aalonsopuig/Retrobot/Media/Foto 16-07-11 15 34 50.jpeg

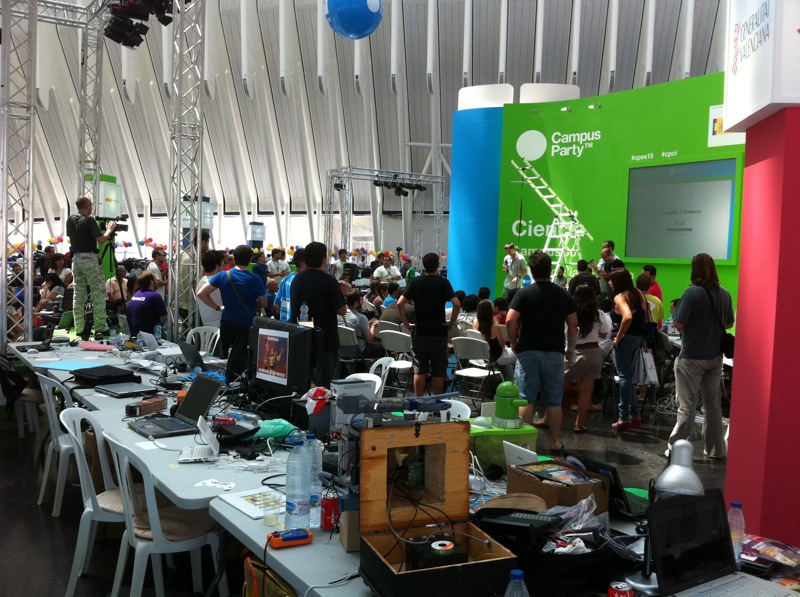
Media/Foto 16-07-11 15 34 50.jpeg
