aalonsopuig/Retrobot/Media/Foto 16-07-11 15 41 18.jpeg

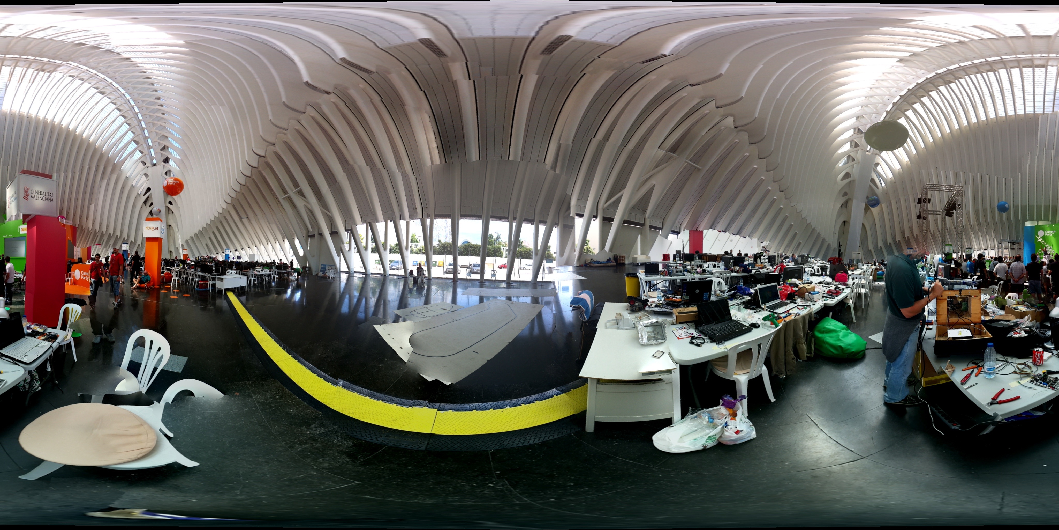
Media/Foto 16-07-11 15 41 18.jpeg
