aalonsopuig/Retrobot/Media/Foto 18-07-11 12 18 01.jpeg

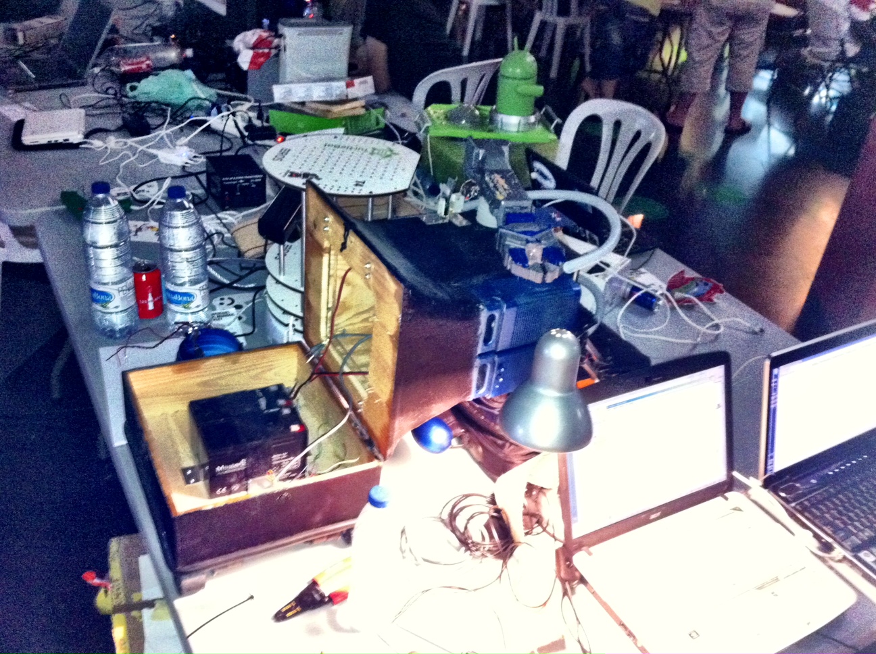
Media/Foto 18-07-11 12 18 01.jpeg
