aalonsopuig/Retrobot/Media/FotoEnCampus.jpg

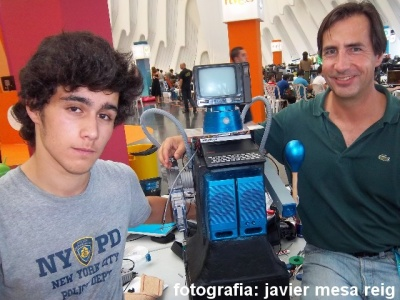
Media/FotoEnCampus.jpg
