aalonsopuig/Retrobot/Media/Imagen 099.jpg

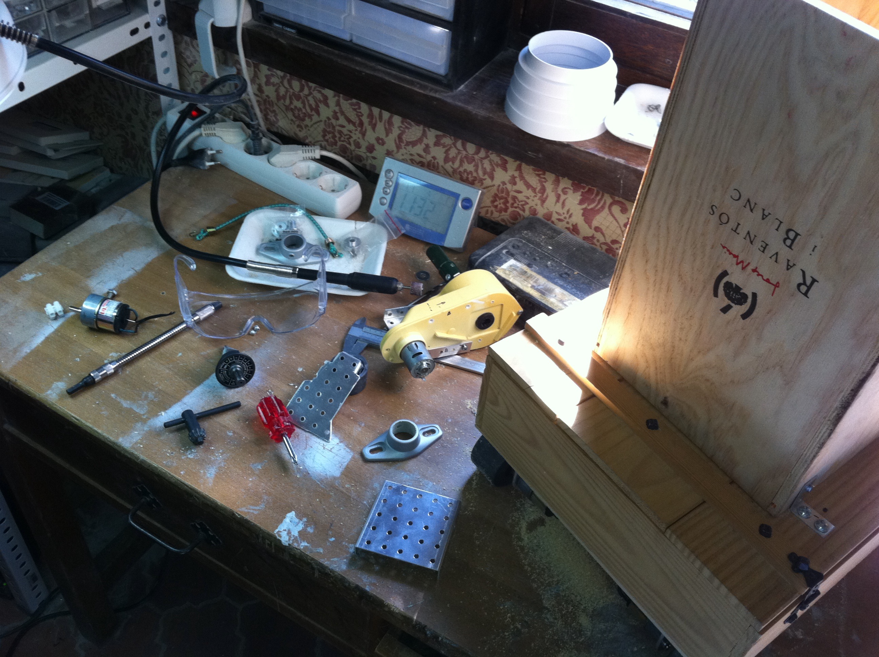
Media/Imagen 099.jpg
