aalonsopuig/Retrobot/Media/Imagen 124.jpg

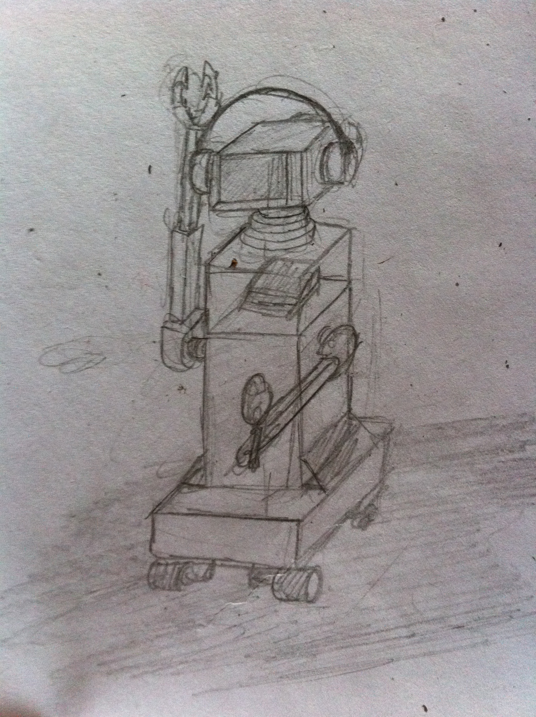
Media/Imagen 124.jpg
