aalonsopuig/Retrobot/Media/Imagen 129.jpg

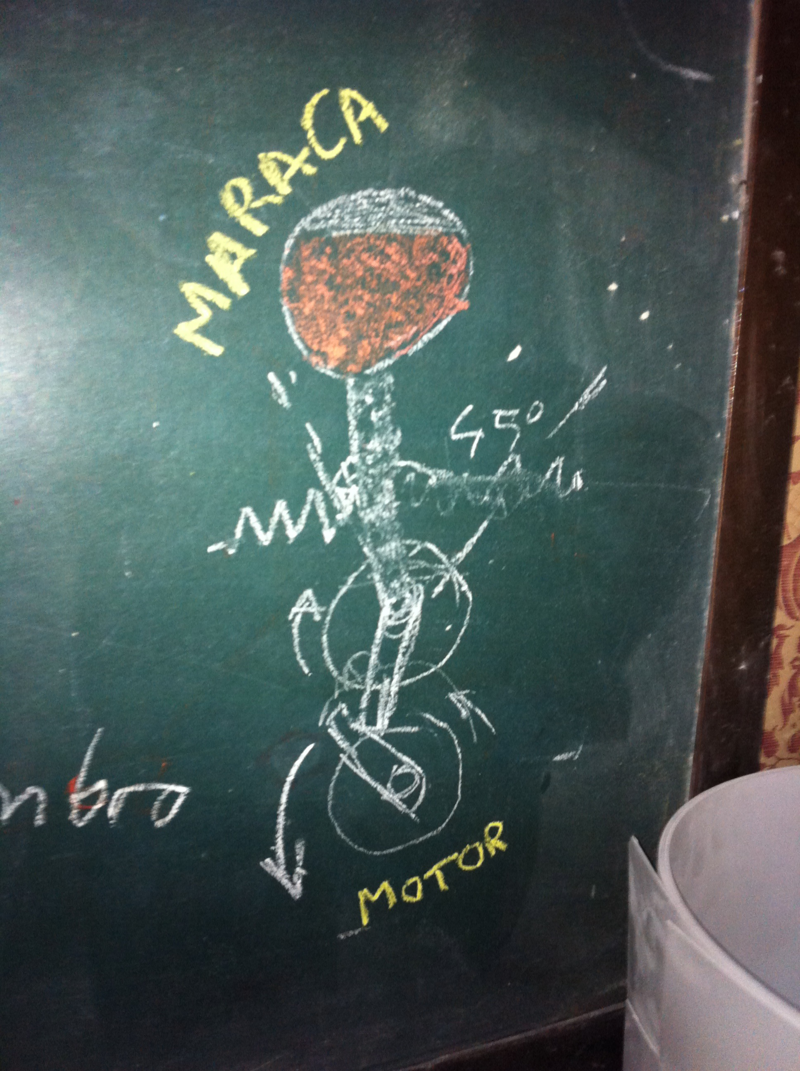
Media/Imagen 129.jpg
