aalonsopuig/Retrobot/Media/Retrobot_aquitectura.jpg

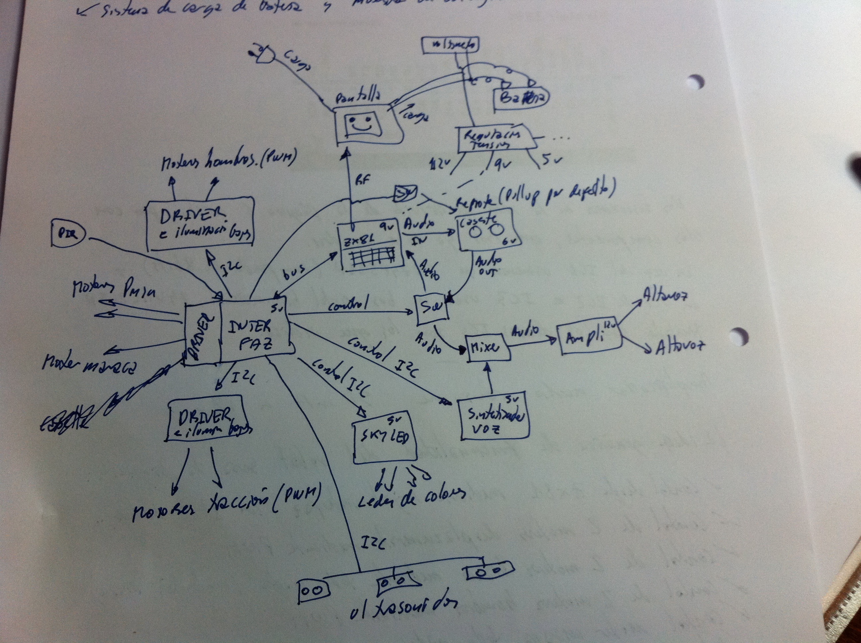
Media/Retrobot_aquitectura.jpg
