aalonsopuig/Retrobot/ZX81/Expansion Bus.jpg

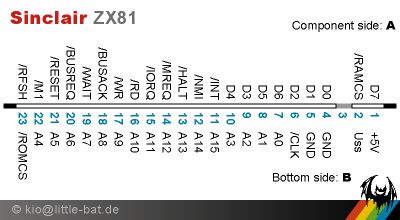
ZX81/Expansion Bus.jpg
