aalonsopuig/Retrobot/Retrobot_SW_ExpansionCard/RetroBot.h

#include <18F2620.h>
#device adc=8

#FUSES NOWDT                    //No Watch Dog Timer
#FUSES WDT128                   //Watch Dog Timer uses 1:128 Postscale
#FUSES HS                       //High speed Osc (> 4mhz)
#FUSES NOPROTECT                //Code not protected from reading
#FUSES IESO                     //Internal External Switch Over mode enabled
#FUSES BROWNOUT                 //Reset when brownout detected
#FUSES BORV21                   //Brownout reset at 2.1V
#FUSES PUT                      //Power Up Timer
#FUSES NOCPD                    //No EE protection
#FUSES STVREN                   //Stack full/underflow will cause reset
#FUSES NODEBUG                  //No Debug mode for ICD
#FUSES NOLVP                    //No Low Voltage Programming on B3(PIC16) or B5(PIC18)
#FUSES NOWRT                    //Program memory not write protected
#FUSES NOWRTD                   //Data EEPROM not write protected
#FUSES NOEBTR                   //Memory not protected from table reads
#FUSES NOCPB                    //No Boot Block code protection
#FUSES NOEBTRB                  //Boot block not protected from table reads
#FUSES NOWRTC                   //configuration not registers write protected
#FUSES NOWRTB                   //Boot block not write protected
#FUSES FCMEN                    //Fail-safe clock monitor enabled
#FUSES XINST                    //Extended set extension and Indexed Addressing mode enabled
//#FUSES PBADEN                   //PORTB pins are configured as analog input channels on RESET
#FUSES LPT1OSC                  //Timer1 configured for low-power operation
#FUSES MCLR                     //Master Clear pin enabled

#use delay(clock=20000000)
#use i2c(Master,Slow,sda=PIN_C4,scl=PIN_C3)
